vamshikrishnaramasamy/oso-keyboard/tools/oracle-review/pcb-extracted-summary.md

# KiCad PCB extracted summary
Source: hardware/kicad/oso75/oso75.kicad_pcb

Board file chars: 3423842
Footprints: 186
Edge.Cuts primitives: 4
Edge bbox: minX=0 maxX=337.088 minY=0 maxY=150.063 width=337.088 height=150.063

## Footprint placement table
ref,value,footprint,layer,x,y,rot
C1,10uF,OSO75:C_0603,F.Cu,152.5,144.5,0
C2,10uF,OSO75:C_0603,F.Cu,141.5,144.5,0
C3,100nF,OSO75:C_0603,F.Cu,178,130.5,0
C4,100nF,OSO75:C_0603,F.Cu,181,142.5,0
D1,1N4148W,OSO75:D_SOD-123_Keyboard,F.Cu,82.175,125.037,0
D2,1N4148W,OSO75:D_SOD-123_Keyboard,F.Cu,101.225,125.037,0
D3,1N4148W,OSO75:D_SOD-123_Keyboard,F.Cu,120.275,125.037,0
D4,1N4148W,OSO75:D_SOD-123_Keyboard,F.Cu,148.85,125.037,0
D5,1N4148W,OSO75:D_SOD-123_Keyboard,F.Cu,167.9,125.037,0
D6,1N4148W,OSO75:D_SOD-123_Keyboard,F.Cu,186.95,125.037,0
D7,1N4148W,OSO75:D_SOD-123_Keyboard,F.Cu,206,125.037,0
D8,1N4148W,OSO75:D_SOD-123_Keyboard,F.Cu,234.575,125.037,0
D9,1N4148W,OSO75:D_SOD-123_Keyboard,F.Cu,253.625,125.037,0
D10,1N4148W,OSO75:D_SOD-123_Keyboard,F.Cu,272.675,125.037,0
D11,1N4148W,OSO75:D_SOD-123_Keyboard,F.Cu,291.725,125.037,0
D12,1N4148W,OSO75:D_SOD-123_Keyboard,F.Cu,25.025,101.225,0
D13,1N4148W,OSO75:D_SOD-123_Keyboard,F.Cu,44.075,101.225,0
D14,1N4148W,OSO75:D_SOD-123_Keyboard,F.Cu,63.125,101.225,0
D15,1N4148W,OSO75:D_SOD-123_Keyboard,F.Cu,82.175,101.225,0
D16,1N4148W,OSO75:D_SOD-123_Keyboard,F.Cu,101.225,101.225,0
D17,1N4148W,OSO75:D_SOD-123_Keyboard,F.Cu,120.275,101.225,0
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
R6,10k,OSO75:R_0603,F.Cu,131.5,138,0
R10,10k,OSO75:R_0603,F.Cu,109.5,138,0
ST1,Stabilizer_Cherry_MX_2.00u,Stabilizer_MX:Stabilizer_Cherry_MX_2.00u,F.Cu,275.7,94.725,180
ST2,Stabilizer_Cherry_MX_2.00u,Stabilizer_MX:Stabilizer_Cherry_MX_2.00u,F.Cu,273.319,56.625,180
ST3,Stabilizer_Cherry_MX_2.00u,Stabilizer_MX:Stabilizer_Cherry_MX_2.00u,F.Cu,30.431,37.575,180
ST4,Stabilizer_Cherry_MX_6.25u,Stabilizer_MX:Stabilizer_Cherry_MX_6.25u,F.Cu,139.969,18.525,180
SW_BOOT,BOOT,OSO75:SW_Tactile_4x3,F.Cu,101.5,138,0
SW_RESET,RESET,OSO75:SW_Tactile_4x3,F.Cu,93.5,138,0
SW1,MX_Hotswap,Switch_MX_Hotswap:SW_Hotswap_Kailh_MX_Plated_1.00u_With_Switch,F.Cu,75.675,118.537,180
SW2,MX_Hotswap,Switch_MX_Hotswap:SW_Hotswap_Kailh_MX_Plated_1.00u_With_Switch,F.Cu,94.725,118.537,180
SW3,MX_Hotswap,Switch_MX_Hotswap:SW_Hotswap_Kailh_MX_Plated_1.00u_With_Switch,F.Cu,113.775,118.537,180
SW4,MX_Hotswap,Switch_MX_Hotswap:SW_Hotswap_Kailh_MX_Plated_1.00u_With_Switch,F.Cu,142.35,118.537,180
SW5,MX_Hotswap,Switch_MX_Hotswap:SW_Hotswap_Kailh_MX_Plated_1.00u_With_Switch,F.Cu,161.4,118.537,180
SW6,MX_Hotswap,Switch_MX_Hotswap:SW_Hotswap_Kailh_MX_Plated_1.00u_With_Switch,F.Cu,180.45,118.537,180
SW7,MX_Hotswap,Switch_MX_Hotswap:SW_Hotswap_Kailh_MX_Plated_1.00u_With_Switch,F.Cu,199.5,118.537,180
SW8,MX_Hotswap,Switch_MX_Hotswap:SW_Hotswap_Kailh_MX_Plated_1.00u_With_Switch,F.Cu,228.075,118.537,180
SW9,MX_Hotswap,Switch_MX_Hotswap:SW_Hotswap_Kailh_MX_Plated_1.00u_With_Switch,F.Cu,247.125,118.537,180
SW10,MX_Hotswap,Switch_MX_Hotswap:SW_Hotswap_Kailh_MX_Plated_1.00u_With_Switch,F.Cu,266.175,118.537,180
SW11,MX_Hotswap,Switch_MX_Hotswap:SW_Hotswap_Kailh_MX_Plated_1.00u_With_Switch,F.Cu,285.225,118.537,180
SW12,MX_Hotswap,Switch_MX_Hotswap:SW_Hotswap_Kailh_MX_Plated_1.00u_With_Switch,F.Cu,18.525,94.725,180
SW13,MX_Hotswap,Switch_MX_Hotswap:SW_Hotswap_Kailh_MX_Plated_1.00u_With_Switch,F.Cu,37.575,94.725,180
SW14,MX_Hotswap,Switch_MX_Hotswap:SW_Hotswap_Kailh_MX_Plated_1.00u_With_Switch,F.Cu,56.625,94.725,180
SW15,MX_Hotswap,Switch_MX_Hotswap:SW_Hotswap_Kailh_MX_Plated_1.00u_With_Switch,F.Cu,75.675,94.725,180
SW16,MX_Hotswap,Switch_MX_Hotswap:SW_Hotswap_Kailh_MX_Plated_1.00u_With_Switch,F.Cu,94.725,94.725,180
SW17,MX_Hotswap,Switch_MX_Hotswap:SW_Hotswap_Kailh_MX_Plated_1.00u_With_Switch,F.Cu,113.775,94.725,180
SW18,MX_Hotswap,Switch_MX_Hotswap:SW_Hotswap_Kailh_MX_Plated_1.00u_With_Switch,F.Cu,132.825,94.725,180
SW19,MX_Hotswap,Switch_MX_Hotswap:SW_Hotswap_Kailh_MX_Plated_1.00u_With_Switch,F.Cu,151.875,94.725,180
SW20,MX_Hotswap,Switch_MX_Hotswap:SW_Hotswap_Kailh_MX_Plated_1.00u_With_Switch,F.Cu,170.925,94.725,180
SW21,MX_Hotswap,Switch_MX_Hotswap:SW_Hotswap_Kailh_MX_Plated_1.00u_With_Switch,F.Cu,189.975,94.725,180
SW22,MX_Hotswap,Switch_MX_Hotswap:SW_Hotswap_Kailh_MX_Plated_1.00u_With_Switch,F.Cu,209.025,94.725,180
SW23,MX_Hotswap,Switch_MX_Hotswap:SW_Hotswap_Kailh_MX_Plated_1.00u_With_Switch,F.Cu,228.075,94.725,180
SW24,MX_Hotswap,Switch_MX_Hotswap:SW_Hotswap_Kailh_MX_Plated_1.00u_With_Switch,F.Cu,247.125,94.725,180
SW25,MX_Hotswap,Switch_MX_Hotswap:SW_Hotswap_Kailh_MX_Plated_1.00u_With_Switch,F.Cu,275.7,94.725,180
SW26,MX_Hotswap,Switch_MX_Hotswap:SW_Hotswap_Kailh_MX_Plated_1.00u_With_Switch,F.Cu,23.288,75.675,180
SW27,MX_Hotswap,Switch_MX_Hotswap:SW_Hotswap_Kailh_MX_Plated_1.00u_With_Switch,F.Cu,47.1,75.675,180
SW28,MX_Hotswap,Switch_MX_Hotswap:SW_Hotswap_Kailh_MX_Plated_1.00u_With_Switch,F.Cu,66.15,75.675,180
SW29,MX_Hotswap,Switch_MX_Hotswap:SW_Hotswap_Kailh_MX_Plated_1.00u_With_Switch,F.Cu,85.2,75.675,180
SW30,MX_Hotswap,Switch_MX_Hotswap:SW_Hotswap_Kailh_MX_Plated_1.00u_With_Switch,F.Cu,104.25,75.675,180
SW31,MX_Hotswap,Switch_MX_Hotswap:SW_Hotswap_Kailh_MX_Plated_1.00u_With_Switch,F.Cu,123.3,75.675,180
SW32,MX_Hotswap,Switch_MX_Hotswap:SW_Hotswap_Kailh_MX_Plated_1.00u_With_Switch,F.Cu,142.35,75.675,180
SW33,MX_Hotswap,Switch_MX_Hotswap:SW_Hotswap_Kailh_MX_Plated_1.00u_With_Switch,F.Cu,161.4,75.675,180
SW34,MX_Hotswap,Switch_MX_Hotswap:SW_Hotswap_Kailh_MX_Plated_1.00u_With_Switch,F.Cu,180.45,75.675,180
SW35,MX_Hotswap,Switch_MX_Hotswap:SW_Hotswap_Kailh_MX_Plated_1.00u_With_Switch,F.Cu,199.5,75.675,180
SW36,MX_Hotswap,Switch_MX_Hotswap:SW_Hotswap_Kailh_MX_Plated_1.00u_With_Switch,F.Cu,218.55,75.675,180
SW37,MX_Hotswap,Switch_MX_Hotswap:SW_Hotswap_Kailh_MX_Plated_1.00u_With_Switch,F.Cu,237.6,75.675,180
SW38,MX_Hotswap,Switch_MX_Hotswap:SW_Hotswap_Kailh_MX_Plated_1.00u_With_Switch,F.Cu,256.65,75.675,180
SW39,MX_Hotswap,Switch_MX_Hotswap:SW_Hotswap_Kailh_MX_Plated_1.00u_With_Switch,F.Cu,280.463,75.675,180
SW40,MX_Hotswap,Switch_MX_Hotswap:SW_Hotswap_Kailh_MX_Plated_1.00u_With_Switch,F.Cu,25.669,56.625,180
SW41,MX_Hotswap,Switch_MX_Hotswap:SW_Hotswap_Kailh_MX_Plated_1.00u_With_Switch,F.Cu,51.863,56.625,180
SW42,MX_Hotswap,Switch_MX_Hotswap:SW_Hotswap_Kailh_MX_Plated_1.00u_With_Switch,F.Cu,70.912,56.625,180
SW43,MX_Hotswap,Switch_MX_Hotswap:SW_Hotswap_Kailh_MX_Plated_1.00u_With_Switch,F.Cu,89.963,56.625,180
SW44,MX_Hotswap,Switch_MX_Hotswap:SW_Hotswap_Kailh_MX_Plated_1.00u_With_Switch,F.Cu,109.013,56.625,180
SW45,MX_Hotswap,Switch_MX_Hotswap:SW_Hotswap_Kailh_MX_Plated_1.00u_With_Switch,F.Cu,128.063,56.625,180
SW46,MX_Hotswap,Switch_MX_Hotswap:SW_Hotswap_Kailh_MX_Plated_1.00u_With_Switch,F.Cu,147.113,56.625,180
SW47,MX_Hotswap,Switch_MX_Hotswap:SW_Hotswap_Kailh_MX_Plated_1.00u_With_Switch,F.Cu,166.162,56.625,180
SW48,MX_Hotswap,Switch_MX_Hotswap:SW_Hotswap_Kailh_MX_Plated_1.00u_With_Switch,F.Cu,185.213,56.625,180
SW49,MX_Hotswap,Switch_MX_Hotswap:SW_Hotswap_Kailh_MX_Plated_1.00u_With_Switch,F.Cu,204.263,56.625,180
SW50,MX_Hotswap,Switch_MX_Hotswap:SW_Hotswap_Kailh_MX_Plated_1.00u_With_Switch,F.Cu,223.313,56.625,180
SW51,MX_Hotswap,Switch_MX_Hotswap:SW_Hotswap_Kailh_MX_Plated_1.00u_With_Switch,F.Cu,242.363,56.625,180
SW52,MX_Hotswap,Switch_MX_Hotswap:SW_Hotswap_Kailh_MX_Plated_1.00u_With_Switch,F.Cu,273.319,56.625,180
SW53,MX_Hotswap,Switch_MX_Hotswap:SW_Hotswap_Kailh_MX_Plated_1.00u_With_Switch,F.Cu,30.431,37.575,180
SW54,MX_Hotswap,Switch_MX_Hotswap:SW_Hotswap_Kailh_MX_Plated_1.00u_With_Switch,F.Cu,61.388,37.575,180
SW55,MX_Hotswap,Switch_MX_Hotswap:SW_Hotswap_Kailh_MX_Plated_1.00u_With_Switch,F.Cu,80.438,37.575,180
SW56,MX_Hotswap,Switch_MX_Hotswap:SW_Hotswap_Kailh_MX_Plated_1.00u_With_Switch,F.Cu,99.487,37.575,180
SW57,MX_Hotswap,Switch_MX_Hotswap:SW_Hotswap_Kailh_MX_Plated_1.00u_With_Switch,F.Cu,118.538,37.575,180
SW58,MX_Hotswap,Switch_MX_Hotswap:SW_Hotswap_Kailh_MX_Plated_1.00u_With_Switch,F.Cu,137.588,37.575,180
SW59,MX_Hotswap,Switch_MX_Hotswap:SW_Hotswap_Kailh_MX_Plated_1.00u_With_Switch,F.Cu,156.638,37.575,180
SW60,MX_Hotswap,Switch_MX_Hotswap:SW_Hotswap_Kailh_MX_Plated_1.00u_With_Switch,F.Cu,175.688,37.575,180
SW61,MX_Hotswap,Switch_MX_Hotswap:SW_Hotswap_Kailh_MX_Plated_1.00u_With_Switch,F.Cu,194.738,37.575,180
SW62,MX_Hotswap,Switch_MX_Hotswap:SW_Hotswap_Kailh_MX_Plated_1.00u_With_Switch,F.Cu,213.787,37.575,180
SW63,MX_Hotswap,Switch_MX_Hotswap:SW_Hotswap_Kailh_MX_Plated_1.00u_With_Switch,F.Cu,232.838,37.575,180
SW64,MX_Hotswap,Switch_MX_Hotswap:SW_Hotswap_Kailh_MX_Plated_1.00u_With_Switch,F.Cu,259.031,37.575,180
SW65,MX_Hotswap,Switch_MX_Hotswap:SW_Hotswap_Kailh_MX_Plated_1.00u_With_Switch,F.Cu,20.906,18.525,180
SW66,MX_Hotswap,Switch_MX_Hotswap:SW_Hotswap_Kailh_MX_Plated_1.00u_With_Switch,F.Cu,44.719,18.525,180
SW67,MX_Hotswap,Switch_MX_Hotswap:SW_Hotswap_Kailh_MX_Plated_1.00u_With_Switch,F.Cu,68.531,18.525,180
SW68,MX_Hotswap,Switch_MX_Hotswap:SW_Hotswap_Kailh_MX_Plated_1.00u_With_Switch,F.Cu,139.969,18.525,180
SW69,MX_Hotswap,Switch_MX_Hotswap:SW_Hotswap_Kailh_MX_Plated_1.00u_With_Switch,F.Cu,211.406,18.525,180
SW70,MX_Hotswap,Switch_MX_Hotswap:SW_Hotswap_Kailh_MX_Plated_1.00u_With_Switch,F.Cu,235.219,18.525,180
SW71,MX_Hotswap,Switch_MX_Hotswap:SW_Hotswap_Kailh_MX_Plated_1.00u_With_Switch,F.Cu,259.031,18.525,180
SW72,MX_Hotswap,Switch_MX_Hotswap:SW_Hotswap_Kailh_MX_Plated_1.00u_With_Switch,F.Cu,318.563,118.537,180
SW73,MX_Hotswap,Switch_MX_Hotswap:SW_Hotswap_Kailh_MX_Plated_1.00u_With_Switch,F.Cu,299.512,94.725,180
SW74,MX_Hotswap,Switch_MX_Hotswap:SW_Hotswap_Kailh_MX_Plated_1.00u_With_Switch,F.Cu,318.563,94.725,180
SW75,MX_Hotswap,Switch_MX_Hotswap:SW_Hotswap_Kailh_MX_Plated_1.00u_With_Switch,F.Cu,299.512,75.675,180
SW76,MX_Hotswap,Switch_MX_Hotswap:SW_Hotswap_Kailh_MX_Plated_1.00u_With_Switch,F.Cu,318.563,75.675,180
SW77,MX_Hotswap,Switch_MX_Hotswap:SW_Hotswap_Kailh_MX_Plated_1.00u_With_Switch,F.Cu,299.512,56.625,180
SW78,MX_Hotswap,Switch_MX_Hotswap:SW_Hotswap_Kailh_MX_Plated_1.00u_With_Switch,F.Cu,318.563,56.625,180
SW79,MX_Hotswap,Switch_MX_Hotswap:SW_Hotswap_Kailh_MX_Plated_1.00u_With_Switch,F.Cu,299.512,37.575,180
SW80,MX_Hotswap,Switch_MX_Hotswap:SW_Hotswap_Kailh_MX_Plated_1.00u_With_Switch,F.Cu,280.463,18.525,180
SW81,MX_Hotswap,Switch_MX_Hotswap:SW_Hotswap_Kailh_MX_Plated_1.00u_With_Switch,F.Cu,299.512,18.525,180
SW82,MX_Hotswap,Switch_MX_Hotswap:SW_Hotswap_Kailh_MX_Plated_1.00u_With_Switch,F.Cu,318.563,18.525,180
U1,ESP32-S3-WROOM-1-N16R8,RF_Module:ESP32-S3-WROOM-1,F.Cu,196,138.8,-90
U3,AP2112K-3.3,OSO75:SOT-23-5_LDO,F.Cu,147,144.5,0
