vamshikrishnaramasamy/oso-keyboard/hardware/cad/generated/oso75_case_plate_preview.png

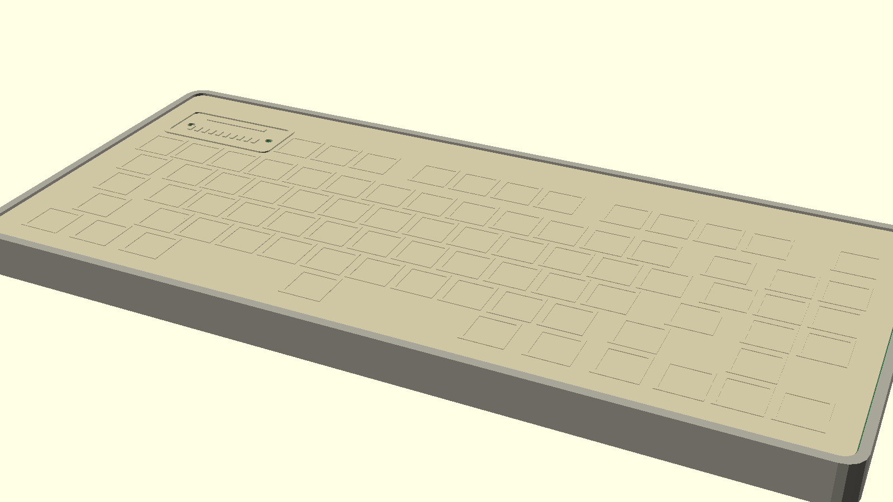
hardware/cad/generated/oso75_case_plate_preview.png
