vamshikrishnaramasamy/oso-keyboard/hardware/cad/generated/oso75_pcb_fit.png

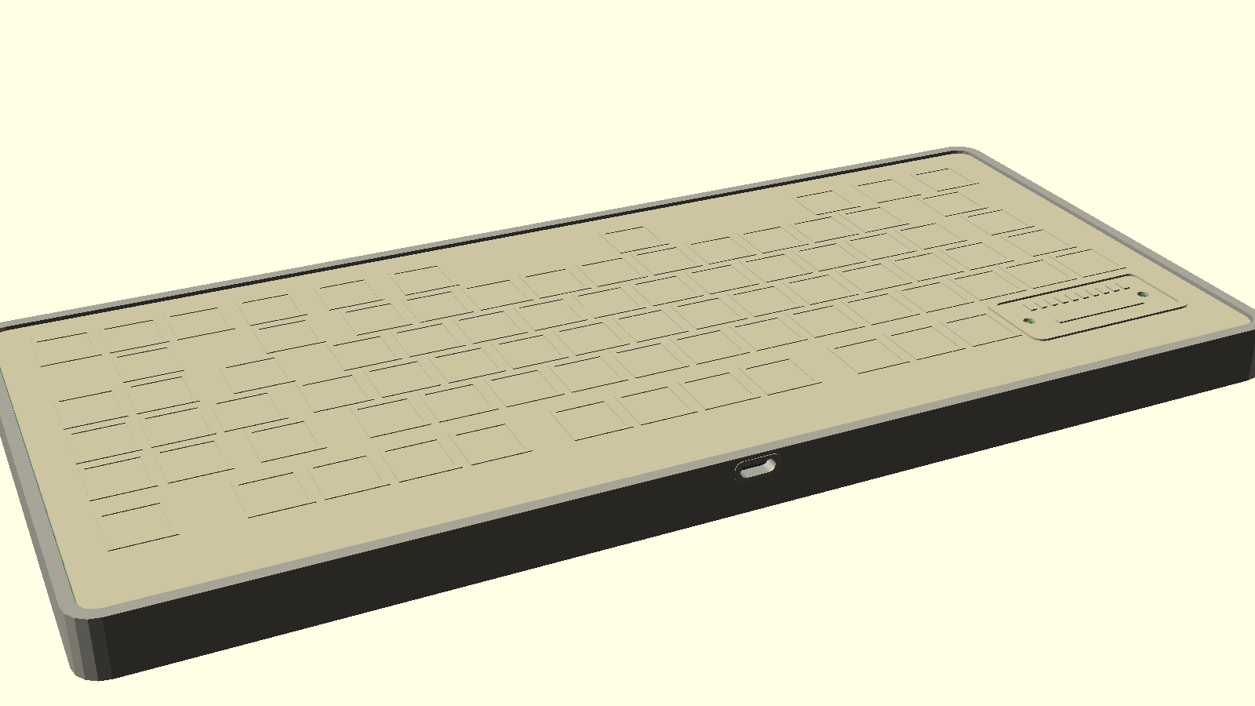
hardware/cad/generated/oso75_pcb_fit.png
