vamshikrishnaramasamy/oso-keyboard/hardware/kicad/oso75/oso75-render.png

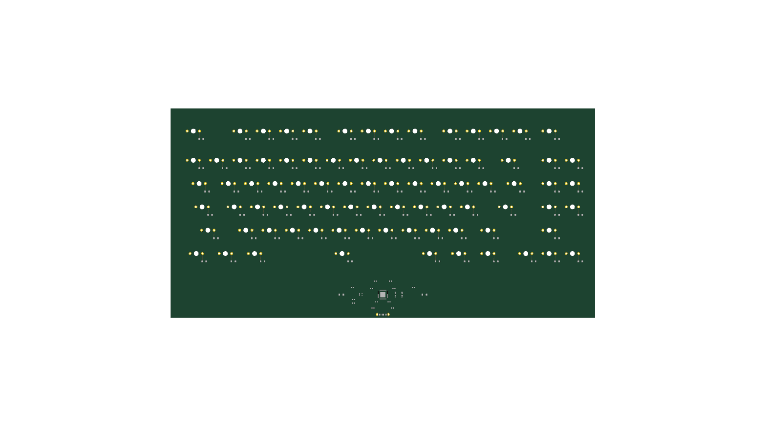
hardware/kicad/oso75/oso75-render.png
