vamshikrishnaramasamy/oso-keyboard/hardware/kicad/oso75/renders/oso75-mirrored-unrouted-top.png

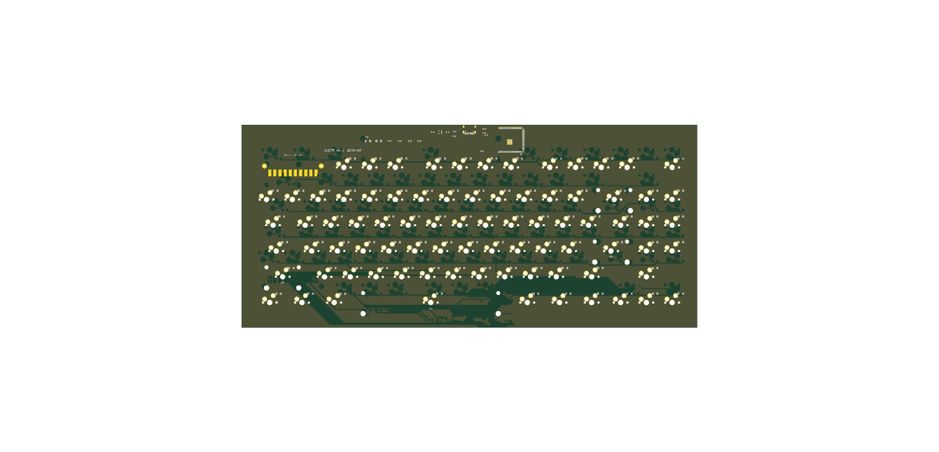
hardware/kicad/oso75/renders/oso75-mirrored-unrouted-top.png
