vamshikrishnaramasamy/oso-keyboard/hardware/kicad/oso75/renders/oso75_bottom.png

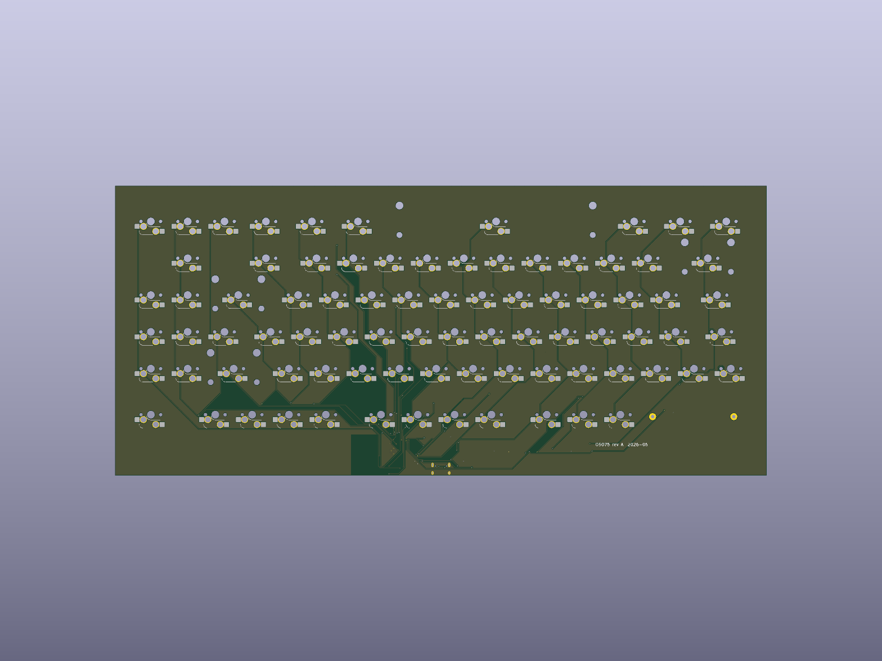
hardware/kicad/oso75/renders/oso75_bottom.png
