vamshikrishnaramasamy/oso-keyboard/docs/lcsc-parts-list.png

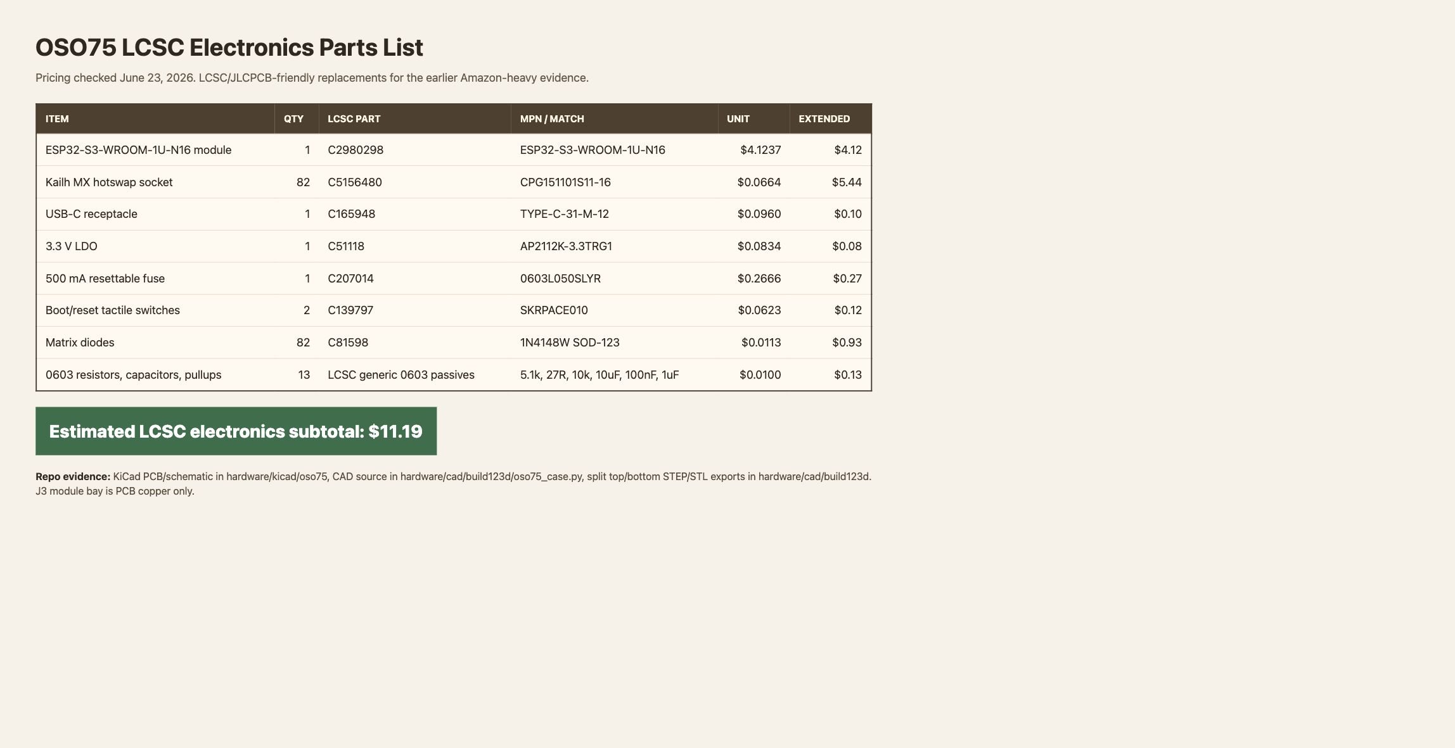
docs/lcsc-parts-list.png
