vamshikrishnaramasamy/oso-keyboard/docs/revised-build-budget.png

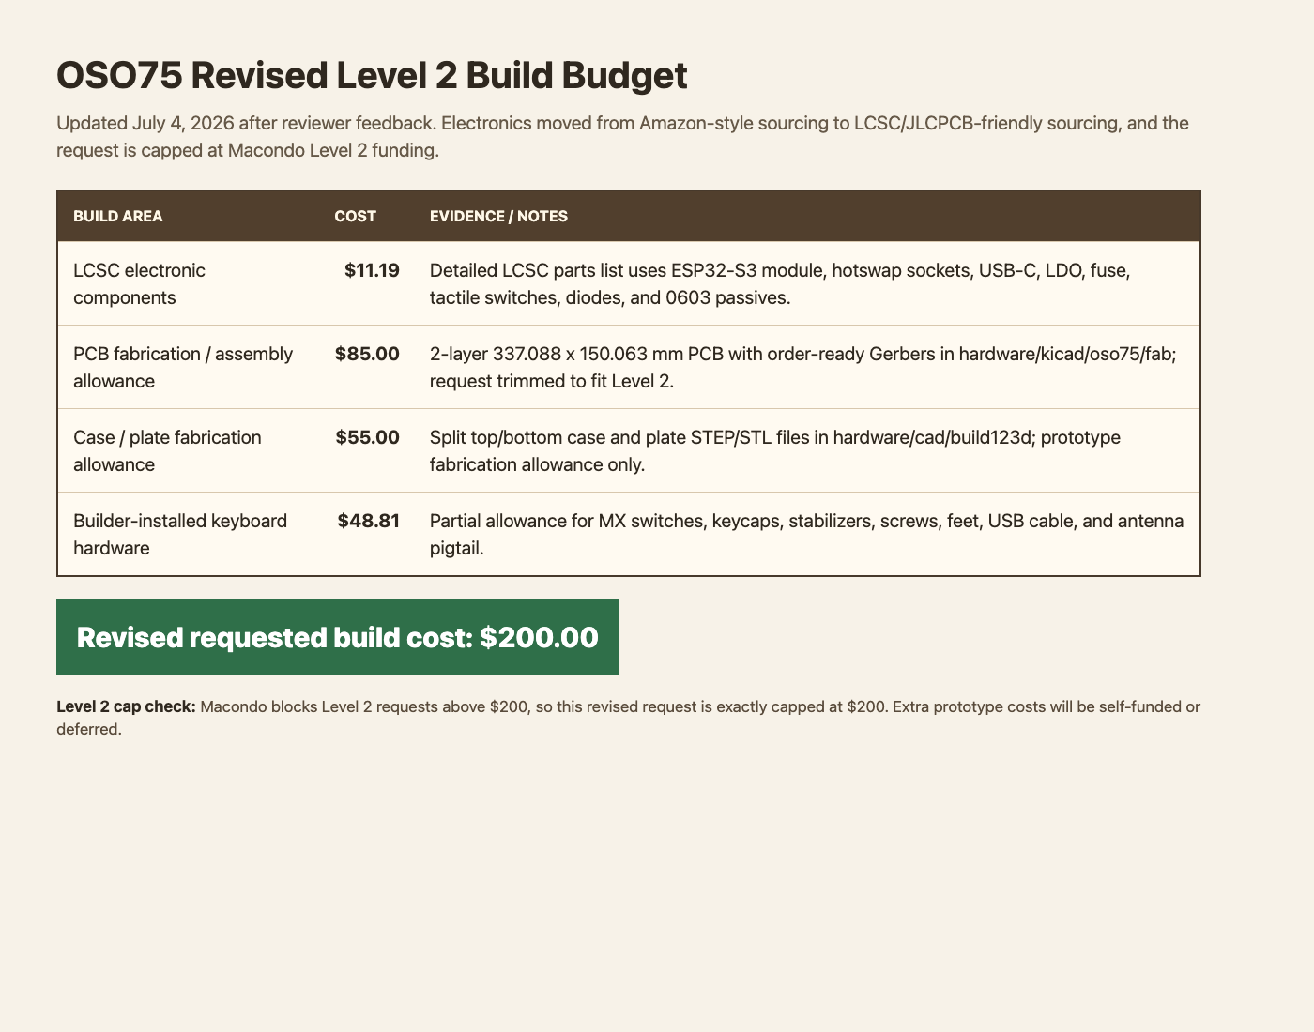
docs/revised-build-budget.png
