vamshikrishnaramasamy/oso-keyboard/hardware/cad/build123d/oso75_preview_back.png

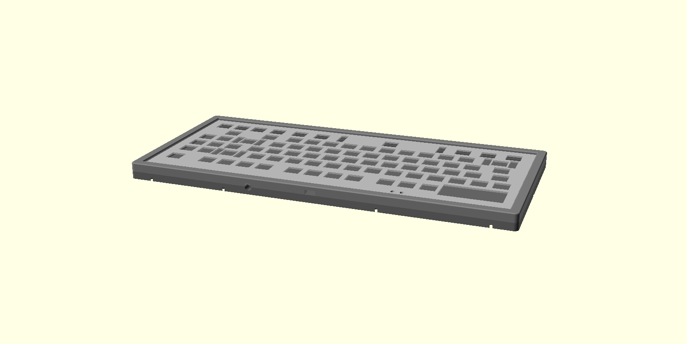
hardware/cad/build123d/oso75_preview_back.png
