vamshikrishnaramasamy/oso-keyboard/hardware/cad/build123d/oso75_preview_bottom.png

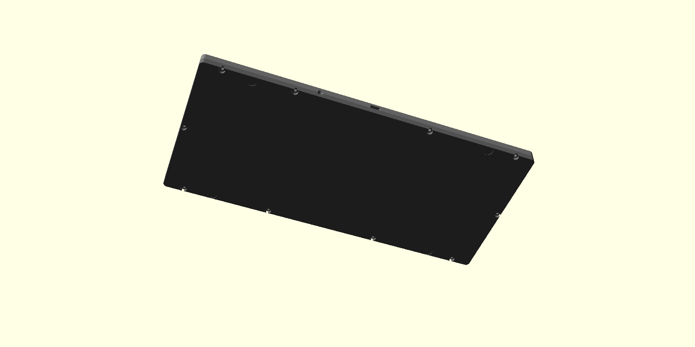
hardware/cad/build123d/oso75_preview_bottom.png
