vamshikrishnaramasamy/oso-keyboard/hardware/cad/build123d/oso75_preview_exploded.png

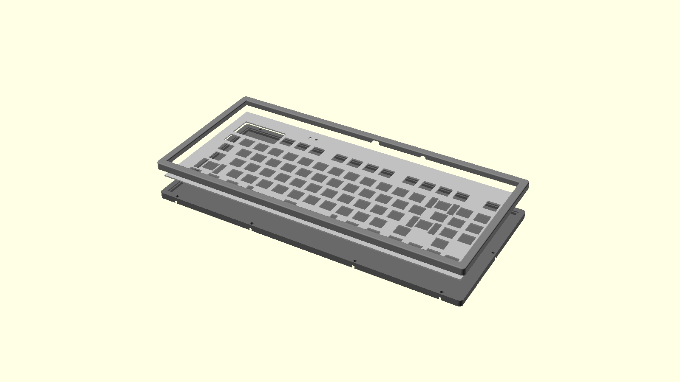
hardware/cad/build123d/oso75_preview_exploded.png
