vamshikrishnaramasamy/oso-keyboard/hardware/kicad/oso75/renders/oso75-final-fixes.png

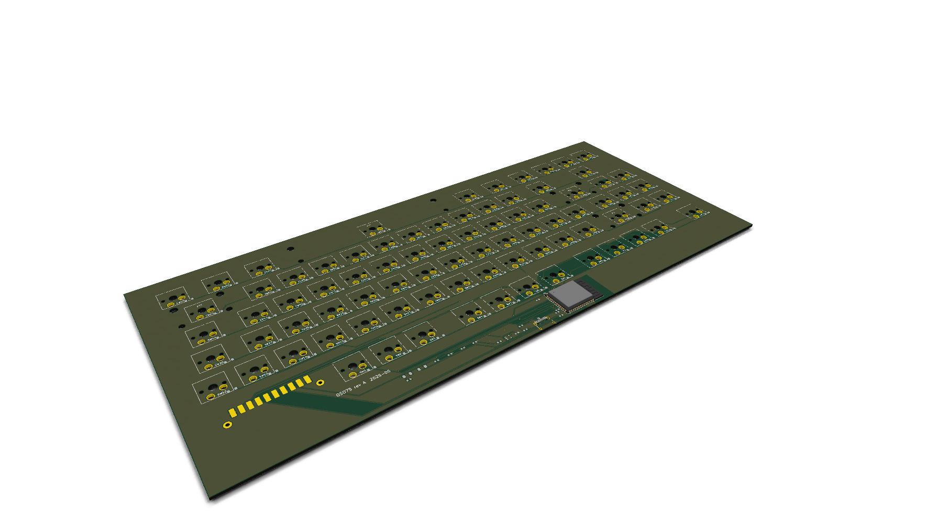
hardware/kicad/oso75/renders/oso75-final-fixes.png
