vamshikrishnaramasamy/oso-keyboard/hardware/kicad/oso75/renders/top-after-cad-layout-fix.png

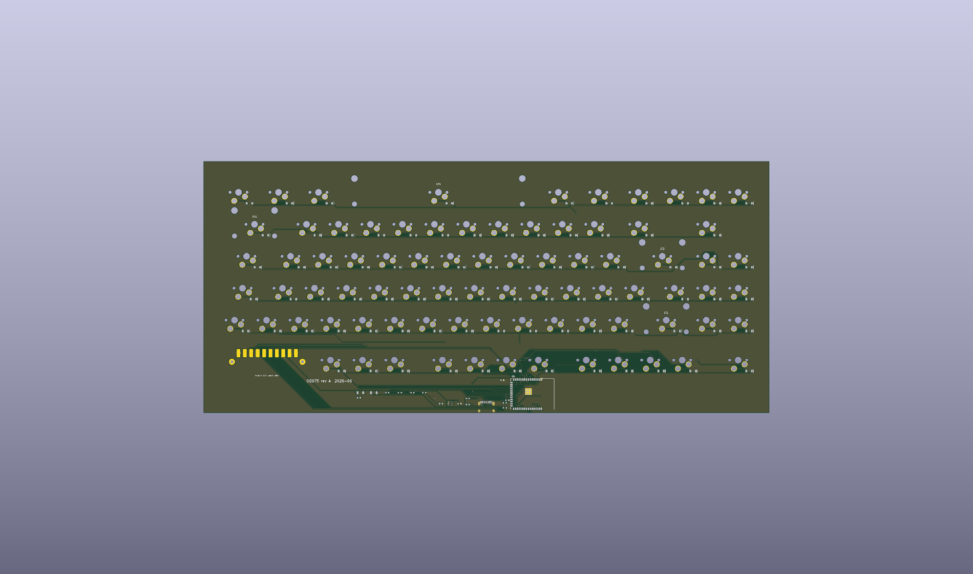
hardware/kicad/oso75/renders/top-after-cad-layout-fix.png
